callaunchpad/magic-camera/3d_case/Slim Raspberry Pi High Quality Camera Case - 4560655/images/1.JPG

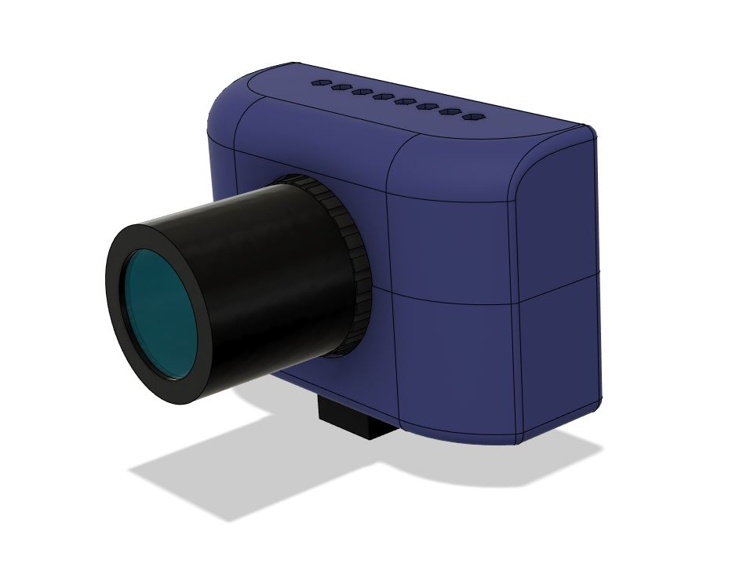
3d_case/Slim Raspberry Pi High Quality Camera Case - 4560655/images/1.JPG
