callaunchpad/magic-camera/3d_case/Slim Raspberry Pi High Quality Camera Case - 4560655/images/IMG_20201221_221621.jpg

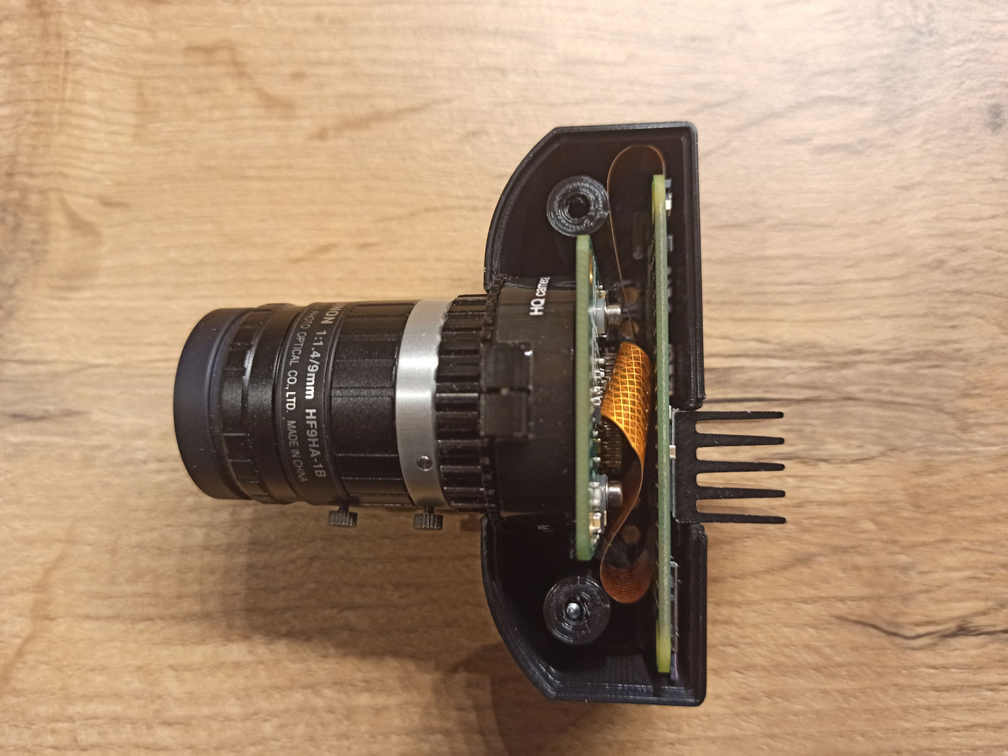
3d_case/Slim Raspberry Pi High Quality Camera Case - 4560655/images/IMG_20201221_221621.jpg
