callaunchpad/magic-camera/annie-selena/poker_night.jpg

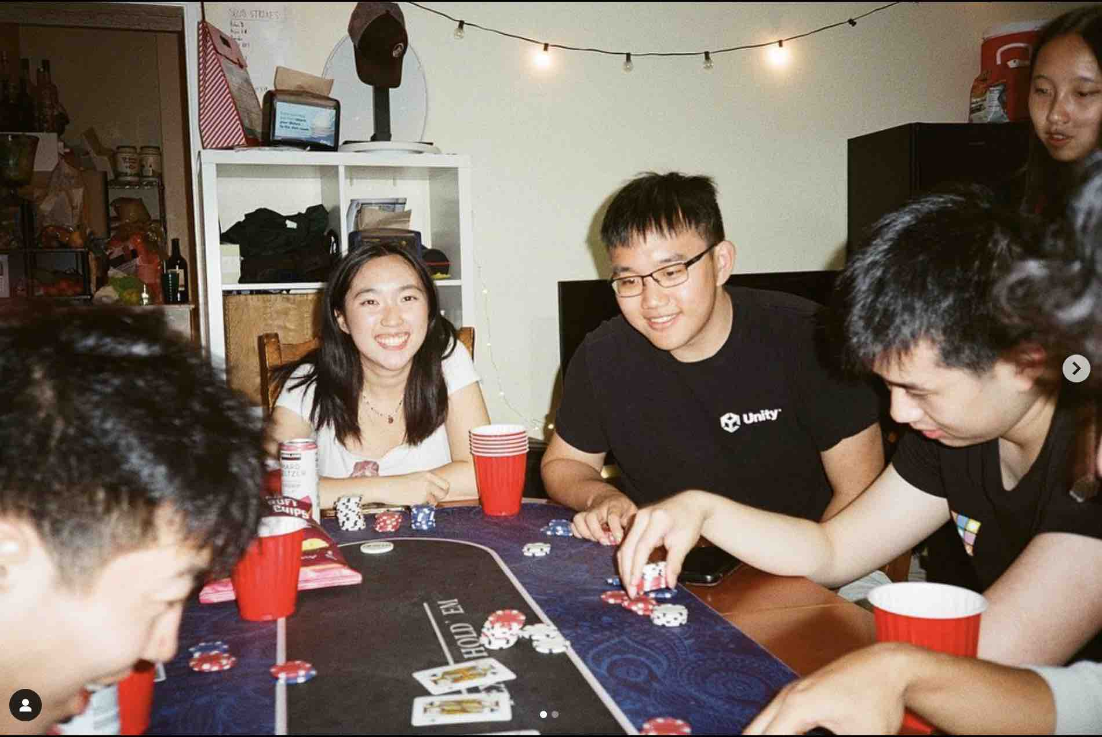
annie-selena/poker_night.jpg
