callaunchpad/magic-camera/arjun/image.png

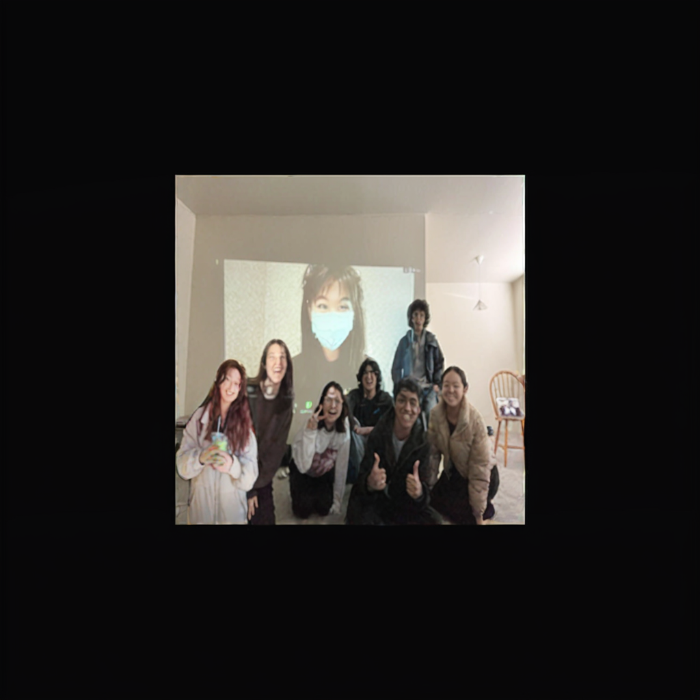
arjun/image.png
