callaunchpad/magic-camera/arjun/patandeshaan.jpg

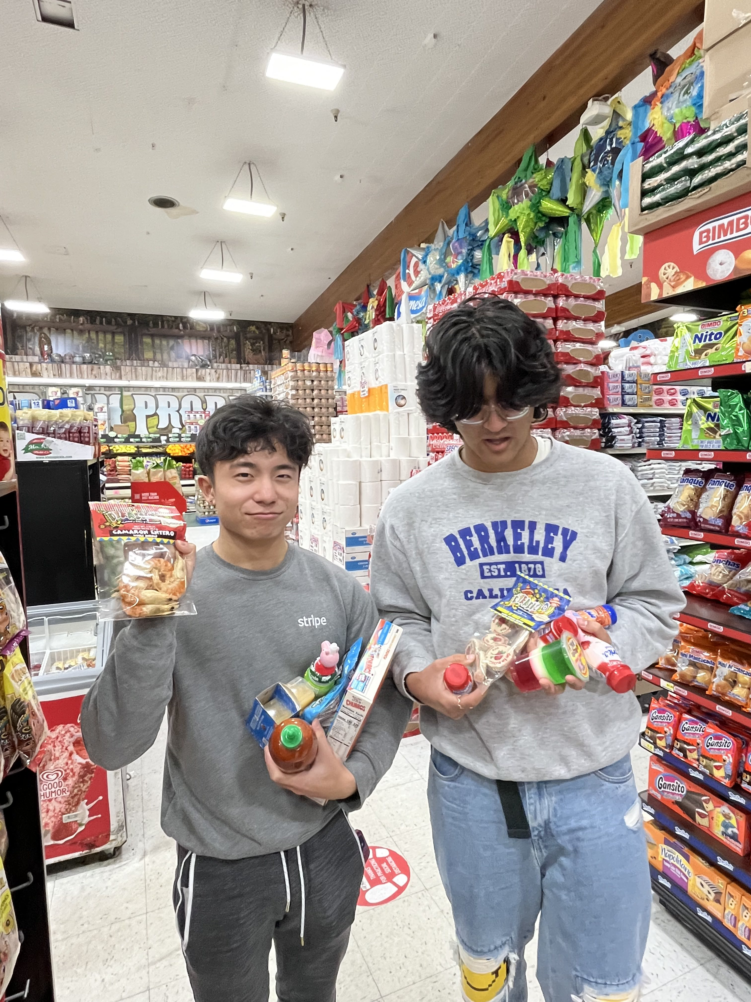
arjun/patandeshaan.jpg
