callaunchpad/magic-camera/arjun/resized_teampic_w_selena.jpg

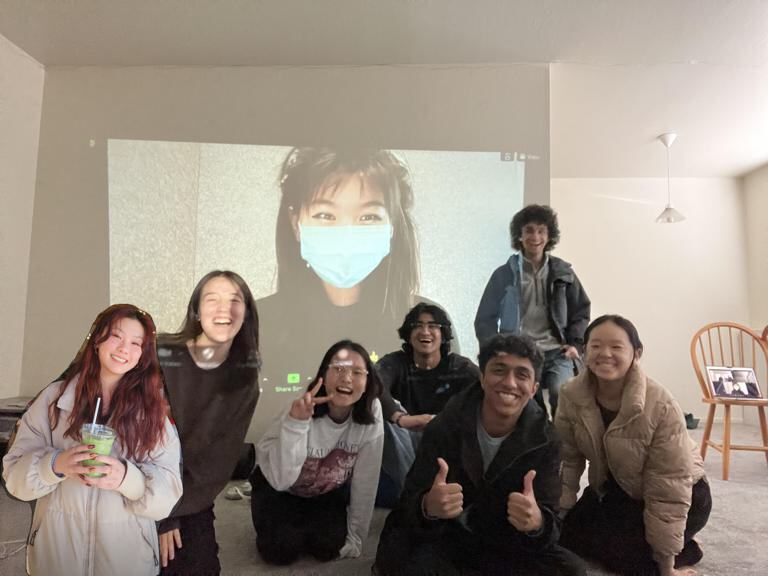
arjun/resized_teampic_w_selena.jpg
