callaunchpad/magic-camera/ericaaudio/compressed_image.jpg

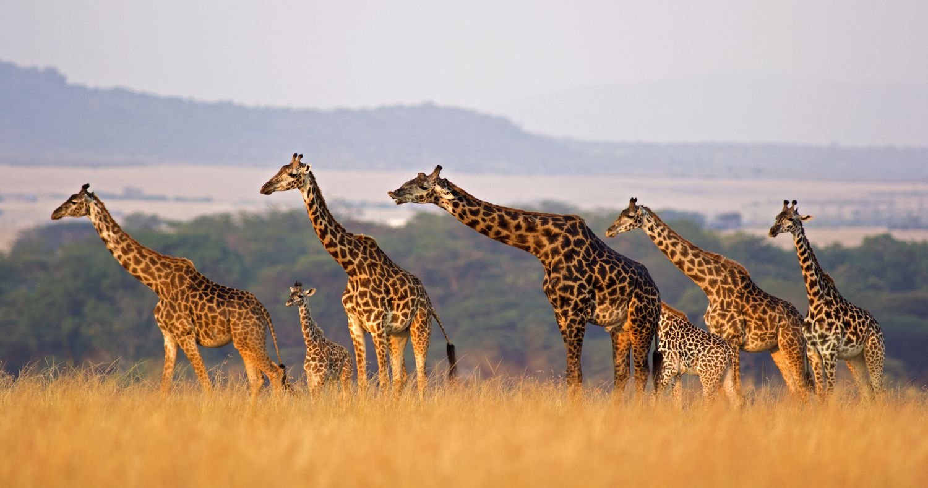
ericaaudio/compressed_image.jpg
