callaunchpad/magic-camera/ericaaudio/dinosaurs.jpg

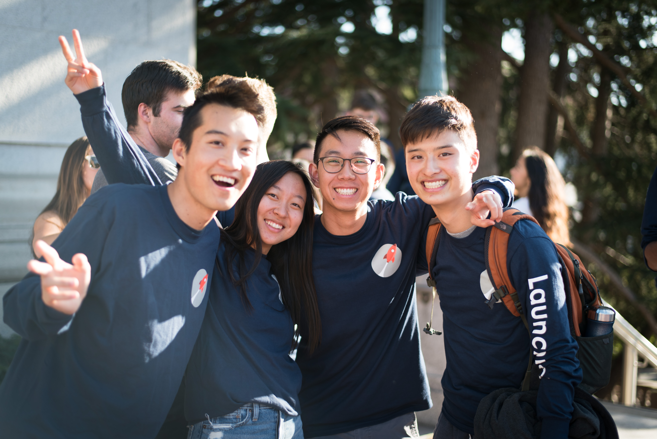
ericaaudio/dinosaurs.jpg
