callaunchpad/magic-camera/ericaaudio/sad.jpg

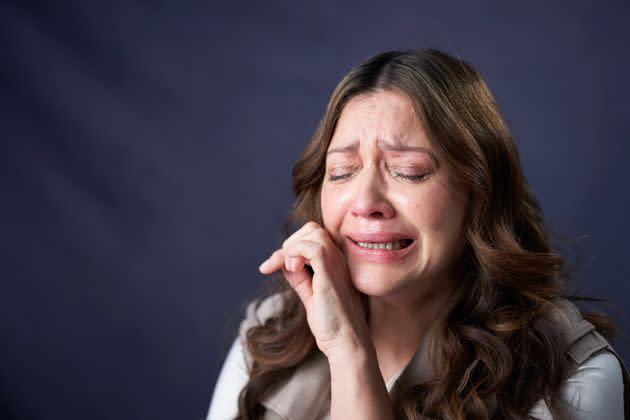
ericaaudio/sad.jpg
