callaunchpad/magic-camera/idkwtqo/googlyeyes.png

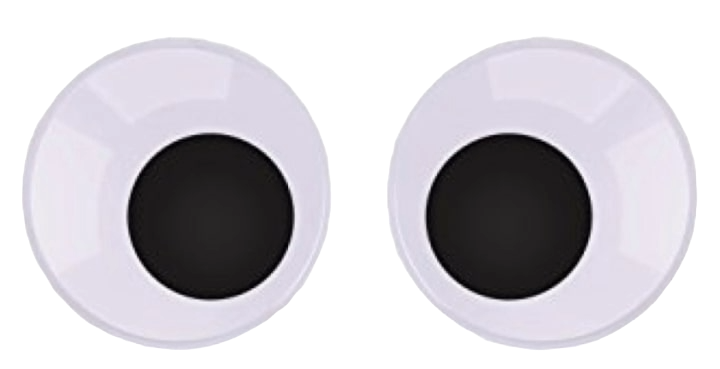
idkwtqo/googlyeyes.png
