callaunchpad/magic-camera/image-server/example_jimmyinator/jimmyli.jpeg

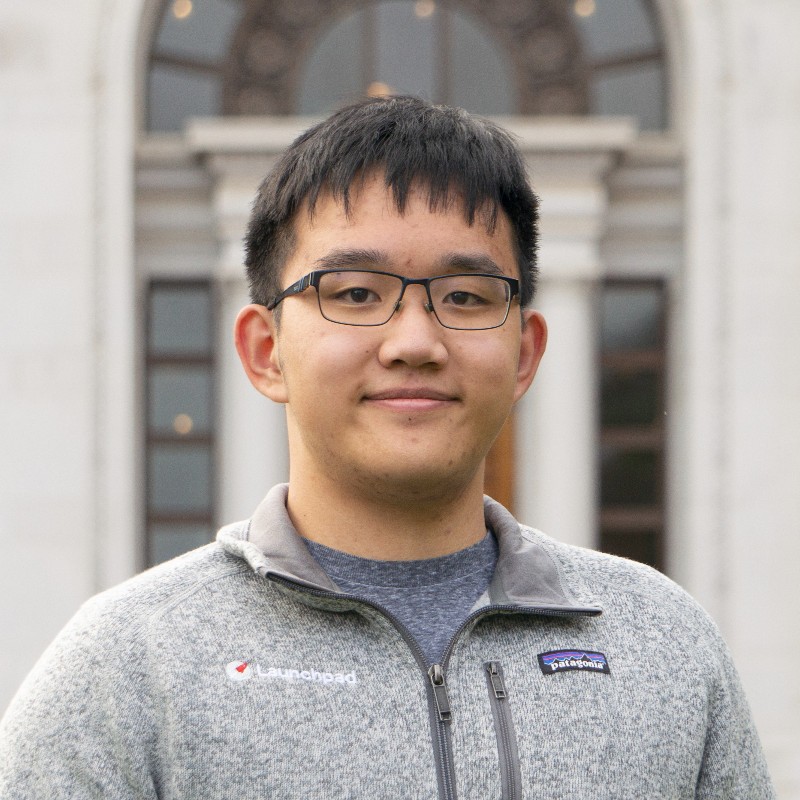
image-server/example_jimmyinator/jimmyli.jpeg
